raffcorreia/samsung-jog-api/memory/MEMORY.md

# Memory Index

- [Project Overview](project_overview.md) — CJ791 JOG emulator: phases 0–15 and 17–18 closed; Phase 16 parked pending hardware access; Phase 19 next for display usability/power hardening; Phase 7 KiCad in progress
- [No cd feedback](feedback_no_cd.md) — Never use cd; pass paths directly to commands (e.g. `npm test --prefix frontend/`)

**Deck UI (kiosk):** Phase 13 complete. Fixed widget geometry on **1280×800** — top bar `48px`, left JOG column `350px`, bottom log band `200px`. JOG and log regions do **not** resize each other when log text grows (scroll inside log). No portal/landing-page chrome; `pi-deck` naming lives in the status/version area, not duplicated as marketing chrome.

**Phase 13 UI decisions:** Clock uses `DSEG7 Classic` seven-segment font and is vertically centered within the unchanged top bar. Settings cog is top-right. LED is gray by default and blue only for future blink/feedback state, not steady `key_led_active`. Record button is a visual stub in the upper-right of the JOG widget column. OSD popup is a reusable portal-based template opened by the JOG dev trigger.

**Phase 14 live log:** Complete. Backend owns live log history in `LiveLogService` with a bounded `220`-entry replay buffer. WebSocket clients receive backend `log/entry` events and replay on connect; frontend only renders received backend entries. UI-originated stub messages go through `POST /api/v1/log`.

**JOG input:** The electrical jog path is **one direction at a time** (same as `JogDrive.release_all` before assert). The UI is **not** multitouch-parallel: a second finger is ignored while the first gesture is active. That matches hardware; it is not a multitouch gesture surface.
