raffcorreia/samsung-jog-api/docs/investigation/phase-24-full-matrix.md

# Phase 24 — Full Register Matrix

All 29 display configurations × 512 registers (256 DDC VCP codes + 256 I2C `0x58` registers).
Values are raw hex as captured. `-` = no scan data for this state/register combination.
DDC columns: VCP codes `0x00`–`0xFF`. I2C columns: `0x58` registers `0x00`–`0xFF`.

| State | DDC 0x0 | DDC 0x1 | DDC 0x2 | DDC 0x3 | DDC 0x4 | DDC 0x5 | DDC 0x6 | DDC 0x7 | DDC 0x8 | DDC 0x9 | DDC 0xa | DDC 0xb | DDC 0xc | DDC 0xd | DDC 0xe | DDC 0xf | DDC 0x10 | DDC 0x11 | DDC 0x12 | DDC 0x13 | DDC 0x14 | DDC 0x15 | DDC 0x16 | DDC 0x17 | DDC 0x18 | DDC 0x19 | DDC 0x1a | DDC 0x1b | DDC 0x1c | DDC 0x1d | DDC 0x1e | DDC 0x1f | DDC 0x20 | DDC 0x21 | DDC 0x22 | DDC 0x23 | DDC 0x24 | DDC 0x25 | DDC 0x26 | DDC 0x27 | DDC 0x28 | DDC 0x29 | DDC 0x2a | DDC 0x2b | DDC 0x2c | DDC 0x2d | DDC 0x2e | DDC 0x2f | DDC 0x30 | DDC 0x31 | DDC 0x32 | DDC 0x33 | DDC 0x34 | DDC 0x35 | DDC 0x36 | DDC 0x37 | DDC 0x38 | DDC 0x39 | DDC 0x3a | DDC 0x3b | DDC 0x3c | DDC 0x3d | DDC 0x3e | DDC 0x3f | DDC 0x40 | DDC 0x41 | DDC 0x42 | DDC 0x43 | DDC 0x44 | DDC 0x45 | DDC 0x46 | DDC 0x47 | DDC 0x48 | DDC 0x49 | DDC 0x4a | DDC 0x4b | DDC 0x4c | DDC 0x4d | DDC 0x4e | DDC 0x4f | DDC 0x50 | DDC 0x51 | DDC 0x52 | DDC 0x53 | DDC 0x54 | DDC 0x55 | DDC 0x56 | DDC 0x57 | DDC 0x58 | DDC 0x59 | DDC 0x5a | DDC 0x5b | DDC 0x5c | DDC 0x5d | DDC 0x5e | DDC 0x5f | DDC 0x60 | DDC 0x61 | DDC 0x62 | DDC 0x63 | DDC 0x64 | DDC 0x65 | DDC 0x66 | DDC 0x67 | DDC 0x68 | DDC 0x69 | DDC 0x6a | DDC 0x6b | DDC 0x6c | DDC 0x6d | DDC 0x6e | DDC 0x6f | DDC 0x70 | DDC 0x71 | DDC 0x72 | DDC 0x73 | DDC 0x74 | DDC 0x75 | DDC 0x76 | DDC 0x77 | DDC 0x78 | DDC 0x79 | DDC 0x7a | DDC 0x7b | DDC 0x7c | DDC 0x7d | DDC 0x7e | DDC 0x7f | DDC 0x80 | DDC 0x81 | DDC 0x82 | DDC 0x83 | DDC 0x84 | DDC 0x85 | DDC 0x86 | DDC 0x87 | DDC 0x88 | DDC 0x89 | DDC 0x8a | DDC 0x8b | DDC 0x8c | DDC 0x8d | DDC 0x8e | DDC 0x8f | DDC 0x90 | DDC 0x91 | DDC 0x92 | DDC 0x93 | DDC 0x94 | DDC 0x95 | DDC 0x96 | DDC 0x97 | DDC 0x98 | DDC 0x99 | DDC 0x9a | DDC 0x9b | DDC 0x9c | DDC 0x9d | DDC 0x9e | DDC 0x9f | DDC 0xa0 | DDC 0xa1 | DDC 0xa2 | DDC 0xa3 | DDC 0xa4 | DDC 0xa5 | DDC 0xa6 | DDC 0xa7 | DDC 0xa8 | DDC 0xa9 | DDC 0xaa | DDC 0xab | DDC 0xac | DDC 0xad | DDC 0xae | DDC 0xaf | DDC 0xb0 | DDC 0xb1 | DDC 0xb2 | DDC 0xb3 | DDC 0xb4 | DDC 0xb5 | DDC 0xb6 | DDC 0xb7 | DDC 0xb8 | DDC 0xb9 | DDC 0xba | DDC 0xbb | DDC 0xbc | DDC 0xbd | DDC 0xbe | DDC 0xbf | DDC 0xc0 | DDC 0xc1 | DDC 0xc2 | DDC 0xc3 | DDC 0xc4 | DDC 0xc5 | DDC 0xc6 | DDC 0xc7 | DDC 0xc8 | DDC 0xc9 | DDC 0xca | DDC 0xcb | DDC 0xcc | DDC 0xcd | DDC 0xce | DDC 0xcf | DDC 0xd0 | DDC 0xd1 | DDC 0xd2 | DDC 0xd3 | DDC 0xd4 | DDC 0xd5 | DDC 0xd6 | DDC 0xd7 | DDC 0xd8 | DDC 0xd9 | DDC 0xda | DDC 0xdb | DDC 0xdc | DDC 0xdd | DDC 0xde | DDC 0xdf | DDC 0xe0 | DDC 0xe1 | DDC 0xe2 | DDC 0xe3 | DDC 0xe4 | DDC 0xe5 | DDC 0xe6 | DDC 0xe7 | DDC 0xe8 | DDC 0xe9 | DDC 0xea | DDC 0xeb | DDC 0xec | DDC 0xed | DDC 0xee | DDC 0xef | DDC 0xf0 | DDC 0xf1 | DDC 0xf2 | DDC 0xf3 | DDC 0xf4 | DDC 0xf5 | DDC 0xf6 | DDC 0xf7 | DDC 0xf8 | DDC 0xf9 | DDC 0xfa | DDC 0xfb | DDC 0xfc | DDC 0xfd | DDC 0xfe | DDC 0xff | I2C 0x0 | I2C 0x1 | I2C 0x2 | I2C 0x3 | I2C 0x4 | I2C 0x5 | I2C 0x6 | I2C 0x7 | I2C 0x8 | I2C 0x9 | I2C 0xa | I2C 0xb | I2C 0xc | I2C 0xd | I2C 0xe | I2C 0xf | I2C 0x10 | I2C 0x11 | I2C 0x12 | I2C 0x13 | I2C 0x14 | I2C 0x15 | I2C 0x16 | I2C 0x17 | I2C 0x18 | I2C 0x19 | I2C 0x1a | I2C 0x1b | I2C 0x1c | I2C 0x1d | I2C 0x1e | I2C 0x1f | I2C 0x20 | I2C 0x21 | I2C 0x22 | I2C 0x23 | I2C 0x24 | I2C 0x25 | I2C 0x26 | I2C 0x27 | I2C 0x28 | I2C 0x29 | I2C 0x2a | I2C 0x2b | I2C 0x2c | I2C 0x2d | I2C 0x2e | I2C 0x2f | I2C 0x30 | I2C 0x31 | I2C 0x32 | I2C 0x33 | I2C 0x34 | I2C 0x35 | I2C 0x36 | I2C 0x37 | I2C 0x38 | I2C 0x39 | I2C 0x3a | I2C 0x3b | I2C 0x3c | I2C 0x3d | I2C 0x3e | I2C 0x3f | I2C 0x40 | I2C 0x41 | I2C 0x42 | I2C 0x43 | I2C 0x44 | I2C 0x45 | I2C 0x46 | I2C 0x47 | I2C 0x48 | I2C 0x49 | I2C 0x4a | I2C 0x4b | I2C 0x4c | I2C 0x4d | I2C 0x4e | I2C 0x4f | I2C 0x50 | I2C 0x51 | I2C 0x52 | I2C 0x53 | I2C 0x54 | I2C 0x55 | I2C 0x56 | I2C 0x57 | I2C 0x58 | I2C 0x59 | I2C 0x5a | I2C 0x5b | I2C 0x5c | I2C 0x5d | I2C 0x5e | I2C 0x5f | I2C 0x60 | I2C 0x61 | I2C 0x62 | I2C 0x63 | I2C 0x64 | I2C 0x65 | I2C 0x66 | I2C 0x67 | I2C 0x68 | I2C 0x69 | I2C 0x6a | I2C 0x6b | I2C 0x6c | I2C 0x6d | I2C 0x6e | I2C 0x6f | I2C 0x70 | I2C 0x71 | I2C 0x72 | I2C 0x73 | I2C 0x74 | I2C 0x75 | I2C 0x76 | I2C 0x77 | I2C 0x78 | I2C 0x79 | I2C 0x7a | I2C 0x7b | I2C 0x7c | I2C 0x7d | I2C 0x7e | I2C 0x7f | I2C 0x80 | I2C 0x81 | I2C 0x82 | I2C 0x83 | I2C 0x84 | I2C 0x85 | I2C 0x86 | I2C 0x87 | I2C 0x88 | I2C 0x89 | I2C 0x8a | I2C 0x8b | I2C 0x8c | I2C 0x8d | I2C 0x8e | I2C 0x8f | I2C 0x90 | I2C 0x91 | I2C 0x92 | I2C 0x93 | I2C 0x94 | I2C 0x95 | I2C 0x96 | I2C 0x97 | I2C 0x98 | I2C 0x99 | I2C 0x9a | I2C 0x9b | I2C 0x9c | I2C 0x9d | I2C 0x9e | I2C 0x9f | I2C 0xa0 | I2C 0xa1 | I2C 0xa2 | I2C 0xa3 | I2C 0xa4 | I2C 0xa5 | I2C 0xa6 | I2C 0xa7 | I2C 0xa8 | I2C 0xa9 | I2C 0xaa | I2C 0xab | I2C 0xac | I2C 0xad | I2C 0xae | I2C 0xaf | I2C 0xb0 | I2C 0xb1 | I2C 0xb2 | I2C 0xb3 | I2C 0xb4 | I2C 0xb5 | I2C 0xb6 | I2C 0xb7 | I2C 0xb8 | I2C 0xb9 | I2C 0xba | I2C 0xbb | I2C 0xbc | I2C 0xbd | I2C 0xbe | I2C 0xbf | I2C 0xc0 | I2C 0xc1 | I2C 0xc2 | I2C 0xc3 | I2C 0xc4 | I2C 0xc5 | I2C 0xc6 | I2C 0xc7 | I2C 0xc8 | I2C 0xc9 | I2C 0xca | I2C 0xcb | I2C 0xcc | I2C 0xcd | I2C 0xce | I2C 0xcf | I2C 0xd0 | I2C 0xd1 | I2C 0xd2 | I2C 0xd3 | I2C 0xd4 | I2C 0xd5 | I2C 0xd6 | I2C 0xd7 | I2C 0xd8 | I2C 0xd9 | I2C 0xda | I2C 0xdb | I2C 0xdc | I2C 0xdd | I2C 0xde | I2C 0xdf | I2C 0xe0 | I2C 0xe1 | I2C 0xe2 | I2C 0xe3 | I2C 0xe4 | I2C 0xe5 | I2C 0xe6 | I2C 0xe7 | I2C 0xe8 | I2C 0xe9 | I2C 0xea | I2C 0xeb | I2C 0xec | I2C 0xed | I2C 0xee | I2C 0xef | I2C 0xf0 | I2C 0xf1 | I2C 0xf2 | I2C 0xf3 | I2C 0xf4 | I2C 0xf5 | I2C 0xf6 | I2C 0xf7 | I2C 0xf8 | I2C 0xf9 | I2C 0xfa | I2C 0xfb | I2C 0xfc | I2C 0xfd | I2C 0xfe | I2C 0xff |
| --- | --- | --- | --- | --- | --- | --- | --- | --- | --- | --- | --- | --- | --- | --- | --- | --- | --- | --- | --- | --- | --- | --- | --- | --- | --- | --- | --- | --- | --- | --- | --- | --- | --- | --- | --- | --- | --- | --- | --- | --- | --- | --- | --- | --- | --- | --- | --- | --- | --- | --- | --- | --- | --- | --- | --- | --- | --- | --- | --- | --- | --- | --- | --- | --- | --- | --- | --- | --- | --- | --- | --- | --- | --- | --- | --- | --- | --- | --- | --- | --- | --- | --- | --- | --- | --- | --- | --- | --- | --- | --- | --- | --- | --- | --- | --- | --- | --- | --- | --- | --- | --- | --- | --- | --- | --- | --- | --- | --- | --- | --- | --- | --- | --- | --- | --- | --- | --- | --- | --- | --- | --- | --- | --- | --- | --- | --- | --- | --- | --- | --- | --- | --- | --- | --- | --- | --- | --- | --- | --- | --- | --- | --- | --- | --- | --- | --- | --- | --- | --- | --- | --- | --- | --- | --- | --- | --- | --- | --- | --- | --- | --- | --- | --- | --- | --- | --- | --- | --- | --- | --- | --- | --- | --- | --- | --- | --- | --- | --- | --- | --- | --- | --- | --- | --- | --- | --- | --- | --- | --- | --- | --- | --- | --- | --- | --- | --- | --- | --- | --- | --- | --- | --- | --- | --- | --- | --- | --- | --- | --- | --- | --- | --- | --- | --- | --- | --- | --- | --- | --- | --- | --- | --- | --- | --- | --- | --- | --- | --- | --- | --- | --- | --- | --- | --- | --- | --- | --- | --- | --- | --- | --- | --- | --- | --- | --- | --- | --- | --- | --- 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
| Single: TB | - | - | 0x02 | - | - | - | - | - | - | - | - | 0x32 | 40 | - | - | - | 59 | - | 75 | - | 0x04 | - | 70 | - | 70 | - | 70 | - | - | - | - | - | - | - | - | - | - | - | - | - | - | - | - | - | - | - | - | - | - | - | - | - | - | - | - | - | - | - | - | - | - | - | - | - | - | - | - | - | - | - | - | - | - | - | - | - | - | - | - | - | - | - | 0x00 | - | - | - | - | - | - | - | - | - | - | - | - | - | 0x04 | - | 3 | - | - | - | - | - | - | - | - | - | 50 | - | 50 | - | 50 | - | - | - | - | - | - | - | - | - | - | - | - | - | - | - | - | - | - | - | - | - | - | - | - | - | - | - | - | 0x02 | - | - | - | - | - | - | - | - | - | - | - | - | - | - | - | - | - | - | - | - | - | - | - | - | - | - | - | - | 0x00 | - | 23364 | - | 6010 | - | - | - | 0x01 | - | - | - | 0x03 | - | - | - | - | - | - | - | - | - | 200 | - | - | - | - | - | 0x6F | - | 0x12 | 0x20 | 0x02 | - | 0x02 | - | - | - | - | - | - | - | - | - | 0x01 | - | - | - | - | - | 0x02 | - | - | 0x01 | - | - | - | - | - | - | - | - | - | - | - | - | - | - | - | - | - | - | - | - | - | - | - | - | - | - | - | - | - | - | 0x02 | 0x00 | 0x0 | 0x0 | 0x79 | 0x0 | 0x0 | 0x0 | 0x0 | 0x37 | 0x37 | 0x0 | 0x0 | 0x81 | 0xd3 | 0x0 | 0x4 | 0xe0 | 0x3 | 0x13 | 0x0 | 0x0 | 0x0 | 0x0 | 0x0 | 0x0 | 0x0 | 0x0 | 0x0 | 0x0 | 0x0 | 0x0 | 0x0 | 0xee | 0x0 | 0x10 | 0x3 | 0xff | 0x0 | 0x0 | 0x0 | 0x0 | 0x0 | 0x0 | 0x20 | 0x0 | 0x0 | 0x5 | 0x0 | 0x0 | 0x0 | 0x0 | 0x50 | 0x0 | 0x40 | 0x0 | 0x2 | 0x0 | 0x0 | 0x0 | 0x0 | 0x45 | 0xd3 | 0xc7 | 0x6 | 0x0 | 0x84 | 0x84 | 0x84 | 0x0 | 0x0 | 0x0 | 0x0 | 0x9 | 0xf | 0x6 | 0x2 | 0x40 | 0x0 | 0x8 | 0x0 | 0x0 | 0x0 | 0x0 | 0x0 | 0x0 | 0x0 | 0x0 | 0x0 | 0x0 | 0x0 | 0x0 | 0x0 | 0x0 | 0x0 | 0x0 | 0x0 | 0x0 | 0x0 | 0x1 | 0x0 | 0x0 | 0x0 | 0x0 | 0x0 | 0x0 | 0x0 | 0x0 | 0x0 | 0x0 | 0x0 | 0x0 | 0x0 | 0x0 | 0x50 | 0x0 | 0x0 | 0x20 | 0x0 | 0x0 | 0x0 | 0x0 | 0x3 | 0x0 | 0x0 | 0x0 | 0x0 | 0x0 | 0x0 | 0x0 | 0x0 | 0x0 | 0x0 | 0x0 | 0x0 | 0x0 | 0x0 | 0x0 | 0x0 | 0x0 | 0x0 | 0x0 | 0x0 | 0x0 | 0x0 | 0x0 | 0x0 | 0x0 | 0x0 | 0x0 | 0x0 | 0x0 | 0xc0 | 0x0 | 0x0 | 0x0 | 0x0 | 0x0 | 0x0 | 0x0 | 0x0 | 0x4 | 0xef | 0x21 | 0xff | 0xd8 | 0x0 | 0x0 | 0xff | 0xf8 | 0x0 | 0x0 | 0x0 | 0x0 | 0x0 | 0x0 | 0x2 | 0x0 | 0x0 | 0x0 | 0x4 | 0x0 | 0x0 | 0x0 | 0x3 | 0x0 | 0x0 | 0x0 | 0x0 | 0x0 | 0x1 | 0x13 | 0x6f | 0xb | 0x0 | 0x0 | 0x0 | 0x0 | 0x0 | 0x0 | 0x41 | 0x66 | 0x66 | 0x0 | 0x0 | 0x0 | 0x0 | 0x0 | 0x0 | 0x0 | 0x0 | 0x0 | 0x0 | 0x0 | 0x0 | 0x0 | 0x0 | 0x3 | 0x3 | 0x3 | 0x3 | 0x3 | 0x3 | 0x3 | 0x3 | 0x3 | 0xf4 | 0x0 | 0x0 | 0x0 | 0x0 | 0x0 | 0x0 | 0x0 | 0x0 | 0x0 | 0x0 | 0x0 | 0x0 | 0x0 | 0x0 | 0x0 | 0x10 | 0x32 | 0x54 | 0x76 | 0x10 | 0x32 | 0x54 | 0x98 | 0x10 | 0x32 | 0x54 | 0x76 | 0x0 | 0x0 | 0x1 | 0x45 |
| PBP — DP left / HDMI right | - | - | 0x02 | - | - | - | - | - | - | - | - | 0x32 | 40 | - | - | - | 0x3B | - | 0x4B | - | 0x04 | - | 70 | - | 70 | - | 70 | - | - | - | - | - | - | - | - | - | - | - | - | - | - | - | - | - | - | - | - | - | - | - | - | - | - | - | - | - | - | - | - | - | - | - | - | - | - | - | - | - | - | - | - | - | - | - | - | - | - | - | - | - | - | - | 0x00 | - | - | - | - | - | - | - | - | - | - | - | - | - | 0x03 | - | 0x03 | - | - | - | - | - | - | - | - | - | 50 | - | 50 | - | 50 | - | - | - | - | - | - | - | - | - | - | - | - | - | - | - | - | - | - | - | - | - | - | - | - | - | - | - | - | 0x02 | - | - | - | - | - | - | - | - | - | - | - | - | - | - | - | - | - | - | - | - | - | - | - | - | - | - | - | - | 0x00 | - | 23364 | - | 6010 | - | - | - | 0x01 | - | - | - | 0x03 | - | - | - | - | - | - | - | - | - | 200 | - | - | - | - | - | 0x6F | - | 0x12 | 0x20 | 0x02 | - | 0x02 | - | - | - | - | - | - | - | - | - | 0x01 | - | - | - | - | - | 0x02 | - | - | 0x01 | - | - | - | - | - | - | - | - | - | - | - | - | - | - | - | - | - | - | - | - | - | - | - | - | - | - | - | - | - | - | 0x02 | 0x00 | 0x00 | 0x00 | 0x79 | 0x00 | 0x00 | 0x00 | 0x00 | 0x37 | 0x37 | 0x00 | 0x00 | 0x81 | 0xD3 | 0xFF | 0x04 | 0xE0 | 0x03 | 0x13 | 0x00 | 0x00 | 0x00 | 0x00 | 0x00 | 0x00 | 0x00 | 0x00 | 0x00 | 0x00 | 0x00 | 0x00 | 0x00 | 0xEE | 0x00 | 0x10 | 0x03 | 0xFF | 0x00 | 0x00 | 0x00 | 0x00 | 0x00 | 0x00 | 0x20 | 0x00 | 0x00 | 0x05 | 0x00 | 0x00 | 0x00 | 0x00 | 0x50 | 0x00 |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
