raffcorreia/samsung-jog-api/docs/implementation/phase-22-execution.md

# Phase 22 Execution Record

## Purpose

Track **Phase 22: Physical Display and Pi Power Button** per [Implementation Plan](./plan.md).

## Status

**Complete.** Closed 2026-05-01 at deploy r89 (v0.1.9).

## Working Goal

Define and validate a physical local power-control path: a hardware button for display on/off and a practical strategy for physically waking or powering on the Raspberry Pi when software UI is unavailable.

## Key Questions to Resolve

1. What should one physical button do — display toggle only, or also Pi shutdown/wake?
2. How does Pi 5 handle a physical power button natively?
3. What is the equivalent path for Pi 2?
4. Single button or separate buttons for display vs Pi power?
5. How does the physical button relate to the existing software PowerMenu?

## Pi 5 — Native Power Button Interface

Raspberry Pi 5 has a dedicated **J2** 2-pin header (`PWR_BTN` / `GLOBAL_EN`) wired to the MxL7704 PMIC:

- **While running:** short press triggers a clean OS shutdown (PMIC signals halt)
- **While halted/off:** any press wakes and boots the Pi
- No software configuration required — behaviour is handled entirely by the PMIC and RP1 chip
- A momentary normally-open button across J2 is sufficient

This is the cleanest path: wire one button to J2 and the Pi handles shutdown and wake natively.

## Pi 2 — Power Button Interface

Raspberry Pi 2 has no PMIC or native power-button header. Available options:

| Option | What it does | Limitation |
|---|---|---|
| **RUN pin header** | Resets the CPU (equivalent to pulling RESET low) | Not a clean shutdown; does not wake from a software halt |
| **GPIO shutdown button** | GPIO + software daemon triggers clean shutdown | Cannot wake from halt — Pi is off, GPIO ISR is not running |
| **External power supervisor** | Always-on MCU or relay cuts/restores 5V to Pi | Requires additional always-on hardware circuit |
| **Operational limitation** | Document that Pi 2 must be woken by restoring USB-C power | No extra hardware needed; operator must physically unplug/replug |

## Decisions

_To be filled in during phase execution._

## GPIO Assignments (Phase 22 additions)

| Signal | GPIO (BCM) | Physical pin | Direction |
|---|---|---|---|
| `display_btn` — display toggle button (active low) | GPIO4 | 7 | Input |
| `led_data` — WS2812B LED data out (SPI0 MOSI) | GPIO10 | 19 | Output |

GPIO10 (SPI0 MOSI) is used for WS2812B because Pi 5's RP1 chip does not expose the GPU DMA mailbox required by `rpi_ws281x`.  The SPI bus encodes each WS2812B bit as 8 SPI clock cycles at 6.4 MHz (156.25 ns/cycle), producing the required NRZ waveform entirely in hardware without root or DMA access.  SPI is accessible via `/dev/spidev0.0` on Pi 5.  On Pi 4 and earlier, SPI0 is on the same GPIO10 pin — no wiring change needed between Pi generations.

## Component Designator Map (Phase 22 protoboard additions)

Continues the Phase 21 numbering (last used: Q9, R24, C4, no U or SW designators before this phase).

| Ref | Value | Function |
|-----|---|---|
| `SW1` | Momentary SPST NO | Display toggle button (GPIO4 → GND when pressed) |
| `R25` | 10 kΩ | GPIO4 hardware pull-up to 3.3V |
| `C5` | 100 nF | GPIO4 debounce cap to GND |
| `U2` | SN74AHCT125 | 3.3V→5V level shifter — **removed**; caused random frame corruption. WS2812B driven directly from GPIO10 at 3.3V logic. |

## Protoboard Wiring — Button Circuit

```
+3V3 (pin 1) ──── R25 (10 kΩ) ──── GPIO4 (pin 7) ──── SW1 ──── GND
                                         │
                                    C5 (100 nF)
                                         │
                                        GND
```

- R25: pull-up keeps GPIO4 HIGH when button is not pressed.
- SW1: connects GPIO4 to GND when pressed (active-low input).
- C5: debounce; 100 nF across GPIO4-GND smooths mechanical contact bounce.
- Software uses `gpiozero.Button(4)` with `pull_up=True` (internal + external pull-up).

## Protoboard Wiring — LED Direct Wiring

```
GPIO10 (pin 19, SPI0 MOSI) ──── LED DIN

LED GND → GND rail
LED 5V → 5V rail
```

- GPIO10 drives WS2812B DIN directly at 3.3V logic — no level shifter.
- The SN74AHCT125 level shifter (U2) was removed after testing showed it caused random frame corruption and missed LED updates. WS2812B tolerates 3.3V logic reliably at this cable length.
- Pi 5 uses SPI (not DMA/PWM) because RP1 has no GPU mailbox; `StripDriver` uses `spidev` at 6.4 MHz.
- Each WS2812B bit is encoded as 8 SPI clock cycles (Adafruit NeoPixel encoding: `0xF8`='1', `0xC0`='0').
- Protoboard signal integrity may still be a factor; if corruption returns, consider point-to-point wiring directly from the Pi header to LED DIN.

## PowerMenu Redesign

### Action Dialog

Replace the current two-option dialog (Display / Power off) with three options:

| Option | Size | Behavior |
|---|---|---|
| **Display only** | normal | toggle display on/off (existing path) |
| **Reset** | small | navigate to countdown screen (10 s) → reboot |
| **Power off** | small, dangerous | navigate to confirmation screen → countdown screen (10 s) → halt |

### Confirmation Screen (reusable)

Shown before Power off only. Text must explain that the deck **cannot be restored without physically unplugging and replugging power**. Screen must be implemented as a reusable component parameterized by message, confirm label, and on-confirm action.

### Countdown Screen (reusable — single component)

Single countdown component used by both Reset and Power off paths. Parameters:
- duration (10 s for both actions; previously may have been shorter)
- on-complete action (reboot | halt)
- cancelable (user can go back before countdown expires)

No duplicate countdown screens.

## Evidence Checklist

- ✅ Pi 5 power button behavior defined and documented (J2 header / PMIC — clean shutdown while running, wake from halt)
- ✅ Pi 2 power button strategy decided (operational limitation documented — physically unplug/replug power)
- ✅ Display on/off button wiring defined (SW1 on GPIO4, R25 pull-up, C5 debounce)
- ✅ Single button decided — SW1 handles display toggle; Pi 5 J2 handles Pi power separately
- ✅ Debounce and press-duration requirements defined (hardware RC filter + 50 ms software debounce; 3 s hold threshold)
- ✅ Physical button design does not conflict with GPIO24 display circuit (GPIO4 is independent)
- ✅ PowerMenu action dialog updated: Display / Restart / Power off with correct sizing
- ✅ Power off confirmation uses `ConfirmDialog` component
- ✅ Countdown screen is a single reusable component (10 s, parameterized by action)
- ✅ Reset path: dialog → countdown → reboot works end-to-end
- ✅ Power off path: dialog → confirmation → countdown → halt works end-to-end
- ✅ WS2812B wired on GPIO10 (SPI0 MOSI, pin 19) direct — level shifter removed (caused corruption)
- ✅ `StripDriver` implemented via SPI at 6.4 MHz with per-LED lock arbitration
- ✅ Healthy state (solid green) confirmed on hardware at startup
- ✅ `StripDriver` integrated into service lifecycle; physical button broadcasts deck-only
- ✅ Host health gate passes (verified at close — see snapshot below)

## Host Health Snapshot

Captured 2026-05-01 at deploy r89 (v0.1.9), ~41 min uptime, kiosk idle:

```text
temperature:    49.4 °C
get_throttled:  0x0  (no flags)
uptime:         41 min
load average:   0.33 / 0.14 / 0.09
RAM:            15 GiB total, 773 MiB used, 15 GiB available
swap:           2.0 GiB total, 0 used
disk (/):       58 GiB total, 5.7 GiB used (11%)
pi-deck:        0.1.9+r89, hardware=live, control_state=idle
```

## Power Consumption

Measured 2026-05-01 with protoboard attached (SW1, WS2812B LED, Phase 21 display circuit):

Measurements taken at 5V supply with Pi 5, protoboard, and Waveshare DSI display. Current fluctuates continuously; values are approximate averages.

| Condition | Voltage | Current | Power | Notes |
|---|---|---|---|---|
| Display ON 100%, LED green 100%, 1 browser | 5V | ~1.30A | ~6.5W | |
| Display ON 100%, LED green 1%, 1 browser | 5V | ~1.26A | ~6.3W | LED at 100% adds ~40 mA |
| Display ON 100%, LED green 1%, no browser  | 5V | ~1.22A | ~6.1W | ~40 mA saved closing remote WS connection |
| JOG button press (any direction) | 5V | ~1.47A | ~7.4W | ~250 mA spike during drive actuation; brief |

The JOG spike (~250 mA over idle) is caused by the GPIO drive circuit actuating the monitor's control board contacts. The spike is well within the 3A supply headroom and does not destabilize the Pi. A decoupling capacitor on the Pi's 5V rail is not needed — the supply has ample margin. A 100 µF electrolytic near the drive transistors on the custom PCB is worth adding as a precaution (noted in Phase 7 open items).
