raffcorreia/samsung-jog-api/docs/implementation/phase-4-execution.md

# Phase 4 Execution Record

## Purpose

This document records the execution outcome for `Phase 4: Analog Drive Circuit Design`.

It complements:

- [Implementation Plan](../implementation/plan.md)
- [Solution Overview](../design/solution-overview.md)
- [Phase 2 Execution Record](./phase-2-execution.md)
- [Phase 3 Execution Record](./phase-3-execution.md)
- [Phase 4 Analog Drive BOM](../hardware/analog-drive-bom.md)

## Goal

Design and approve an analog drive path that can safely reproduce the required `JOG` resistor-to-ground states on `KEY_ADC1` and `KEY_ADC2` while preserving the original front-panel `JOG` behavior.

## Reference Diagram

Current analog-drive concept diagram:

Phase 4 analog drive path concept

KiCad design artifacts for implementation:

- KiCad project: [`hardware/kicad/analog-drive/analog-drive.kicad_pro`](../../hardware/kicad/analog-drive/analog-drive.kicad_pro)
- KiCad schematic: [`hardware/kicad/analog-drive/analog-drive.kicad_sch`](../../hardware/kicad/analog-drive/analog-drive.kicad_sch)
- KiCad PCB: [`hardware/kicad/analog-drive/analog-drive.kicad_pcb`](../../hardware/kicad/analog-drive/analog-drive.kicad_pcb)
- KiCad BOM CSV: [`hardware/kicad/analog-drive/analog-drive.bom.csv`](../../hardware/kicad/analog-drive/analog-drive.bom.csv)

## Inputs From Prior Phases

The design is based on these already-confirmed constraints:

- `KEY_ADC1` and `KEY_ADC2` are interpreted by the monitor as resistance-to-ground states.
- `KEY_ADC1` is effectively binary (`idle` vs `center`).
- `KEY_ADC2` requires multiple distinct analog states (`idle`, `left`, `right`, `down`, `up`).
- the original `JOG` board remains physically present and must continue to function.
- observation and drive paths must coexist without bus contention.

## Design Scope

In scope:

- analog drive architecture for `KEY_ADC1` and `KEY_ADC2`
- drive/observe coexistence strategy
- preservation strategy for original `JOG` behavior
- component selection for the drive subcircuit
- analog-drive BOM and review artifacts

Out of scope:

- final integrated board outline and connector families
- final software API surface
- final GPIO numbering decisions

## Candidate Drive Approaches

### Candidate A: GPIO-Selected Discrete Resistor Ladder

Use analog switches to connect pre-selected resistor legs to ground per command.

Pros:

- deterministic resistance states
- straightforward debug with DMM
- minimal software complexity

Cons:

- more passives and routing density
- tolerance-stack management across many discrete values

### Candidate B: Digital Potentiometer Per Channel

Use one digital potentiometer channel per driven signal.

Pros:

- compact resistor-state control via software
- fewer discrete resistor networks

Cons:

- wiper behavior and endpoint resistance may reduce state fidelity
- update timing and nonlinearity may complicate repeatability

### Candidate C: Fail-Safe Per-Leg Analog Switch Drive (Selected)

Use one normally-open analog switch per resistor leg so every commanded resistance-to-ground path is individually off by default.

Pros:

- best fit to asymmetric signal behavior (`KEY_ADC2` multi-state, `KEY_ADC1` binary)
- hardware-default safe state does not depend on mux address decoding during Pi boot or reset
- predictable electrical states with low software ambiguity
- preserves a clear path to later calibration refinement

Cons:

- uses more switch-control GPIOs than a mux-based design
- slightly higher part count than a shared-address mux approach

## Selected Architecture

The selected Phase 4 architecture is a **fail-safe per-leg switched-resistance drive path**:

- `KEY_ADC2`: four independent bilateral analog-switch channels gate four calibrated resistor legs to `GND`, one per logical direction.
- `KEY_ADC1`: dedicated single bilateral analog switch gates the center pull-down leg.
- both channels default to high-impedance (`idle`) when no command is active.
- one command arbiter guarantees mutually exclusive drive state application.
- hardware biasing holds all switch enables in the off state until the host actively asserts a command.
- software-enforced break-before-make timing remains in place as a second line of protection.

## Original `JOG` Preservation Strategy

The original front-panel `JOG` remains connected in parallel with the controller board under these rules:

- controller outputs are never actively driven high onto monitor lines.
- controller only presents controlled resistance-to-ground states.
- controller defaults to high-impedance when idle or faulted.
- firmware arbitration blocks controller-driven actions while local physical manipulation is detected as active.

## Drive/Observe Coexistence Strategy

- observation front end remains high-impedance and passive relative to drive operations.
- software continuously verifies observed line values during drive operations.
- if observed voltages fall outside expected windows, drive is immediately released to high-impedance and the sequence is aborted.

## Verification Approach

The Phase 4 verification approach is:

1. bench-check each commanded resistor state at the monitor-side connector with power off.
2. verify powered-state voltages for each commanded logical action.
3. validate that local `JOG` operation still works with the drive board connected.
4. run repeated command cycles while confirming no stuck-active drive condition.
5. confirm safe release-to-idle behavior on host process termination.

## Deliverables Completed

- reviewed analog-drive topology with explicit switch-to-resistor channel mapping
- cleaned KiCad schematic with explicit monitor and host connector wiring
- corrected the final `KEY_ADC1_BUS`, `KEY_ADC2_BUS`, and connector-ground net assignments in the KiCad schematic
- compact KiCad PCB prototype layout for the analog-drive subcircuit
- attached standard KiCad 3D models to the PCB footprints so populated board rendering works again
- JLC-oriented BOM using tested commercial resistor substitutions and current orderable part numbers
- exported manufacturing artifacts validated by `kicad-cli` gerber, position-file, and board-render generation

## Exit-Criteria Assessment

Phase 4 is complete at the prototype-design level.

The final state now includes:

- a KiCad schematic with explicit monitor and host connector wiring
- a routed KiCad PCB prototype for the analog-drive circuit
- a JLC-oriented BOM for the tested resistor set
- manufacturing artifact export from the board file
- working 3D model references on the PCB footprints

Verification status:

- `kicad-cli sch erc` passes with `0` errors and only library/symbol warnings
- `kicad-cli pcb export gerbers` succeeds
- `kicad-cli pcb export pos` succeeds
- `kicad-cli pcb render` succeeds

Known limitation:

- `kicad-cli pcb drc` crashes in this environment with a KiCad `10.0.0` macOS CLI runtime error (`SwiftNativeNSArray` out-of-range), so a final GUI DRC pass is still required before sending the board to fabrication
- one remaining schematic warning cluster in the `ADC1_CENTER_EN` area should still be reviewed visually in KiCad GUI during the final PCB pass

## Open Items Deferred to Later Phases

- final integrated-board connector and mechanical constraints
- exact software timing constants after hardware-in-loop testing
- validation of the JLC-orderable `U1` substitution on the physical assembled board
- final GUI PCB DRC and visual routing review before fabrication release
