raffcorreia/samsung-jog-api/docs/implementation/phase-17-execution.md

# Phase 17 Execution Record

## Purpose

Record completion of **Phase 17: Development Fixture** per [Implementation Plan](./plan.md).

## Status

**Closed:** 2026-04-20.

Phase 17 was closed as a pragmatic temporary fixture, not as a detailed mechanical-design deliverable.

## Summary

A crude open support was built to keep the monitor and Raspberry Pi together in a repeatable development setup. The fixture is intentionally minimal: it is only meant to hold the monitor/control-deck assembly in a usable position while the project moves into display and touch validation.

The result is sufficient to unblock Phase 18 because the Pi and monitor can now be handled and tested as one development assembly instead of as loose bench hardware.

## Scope Notes

- The fixture is open and temporary.
- The fixture does not attempt final enclosure geometry, cosmetic finish, protective covers, or detailed cable-management design.
- Connector-clearance and strain-relief work remains practical/observational rather than fully documented CAD-level validation.
- Any final enclosure, refined mount, or integrated-board mechanical layout remains deferred.

## Exit Criteria Review

| Criterion | Status |
|---|---|
| Pi and development hardware are held in a stable, repeatable position | Done for temporary development use. |
| Connectors remain serviceable without full disassembly | Accepted for current crude support. Re-check during Phase 18 display installation. |
| Harness routing avoids obvious strain during development handling | Accepted for current crude support. Re-check once DSI display and touch wiring are installed. |
| Pi orientation and detailed clearance rationale are documented | Deferred. The Phase 17 deliverable was intentionally reduced to a crude support so Phase 18 can proceed. |

## Follow-Up

- Re-check cable strain and connector access after the Waveshare display is physically installed.
- Capture any display-specific mechanical constraints in the Phase 18 execution record.
- Defer polished enclosure, covers, and final integrated-board mechanical design to a later enclosure/mechanical phase.
