raffcorreia/samsung-jog-api/docs/investigation/ddc-scan/ddc-scan-20260501-153903-summary.md

# DDC VCP Scan Summary

- **Date:** 2026-05-01 15:43
- **Bus:** I2C-13
- **Codes scanned:** 256 (0x00–0xFF)
- **Codes responding:** 32
- **Log:** `ddc-scan-20260501-153903.jsonl`

## Responding Codes

| Code | Name | Type | Current | Max / SL |
|---|---|---|---|---|
| `0x02` | New Control Value | CNC |  | VCP 02 CNC x00 xff x00 x02 |
| `0x0B` | Color Temperature Increment | CNC |  | VCP 0B CNC xff xff x00 x32 |
| `0x0C` | Color Temperature Request | C | 40 | 170 |
| `0x10` | Brightness | C | 59 | 100 |
| `0x12` | Contrast | C | 75 | 100 |
| `0x14` | Select Color Preset | SNC |  | VCP 14 SNC x04 |
| `0x16` | Red Video Gain | C | 70 | 100 |
| `0x18` | Green Video Gain | C | 70 | 100 |
| `0x1A` | Blue Video Gain | C | 70 | 100 |
| `0x52` | Active Control | CNC |  | VCP 52 CNC x00 xff x00 x00 |
| `0x60` | Input Source | SNC |  | VCP 60 SNC x04 |
| `0x62` | Audio Speaker Volume | C | 3 | 100 |
| `0x6C` | Video Black Level: Red | C | 50 | 100 |
| `0x6E` | Video Black Level: Green | C | 50 | 100 |
| `0x70` | Video Black Level: Blue | C | 50 | 100 |
| `0x8D` | Audio Mute | SNC |  | VCP 8D SNC x02 |
| `0xAA` | Screen Orientation | SNC |  | VCP AA SNC x00 |
| `0xAC` | Horizontal Frequency | C | 23364 | 65281 |
| `0xAE` | Vertical Frequency | C | 6000 | 65535 |
| `0xB2` | Flat Panel Sub-Pixel Layout | SNC |  | VCP B2 SNC x01 |
| `0xB6` | Display Technology Type | SNC |  | VCP B6 SNC x03 |
| `0xC0` | Display Usage Time | C | 200 | 65535 |
| `0xC6` | Application Enable Key | CNC |  | VCP C6 CNC xff xff x00 x6f |
| `0xC8` | Display Controller ID | CNC |  | VCP C8 CNC xff xff x00 x12 |
| `0xC9` | Display Firmware Level | CNC |  | VCP C9 CNC xff xff x01 x20 |
| `0xCA` | OSD/Button Control | SNC |  | VCP CA SNC x02 |
| `0xCC` | OSD Language | SNC |  | VCP CC SNC x02 |
| `0xD6` | Power Mode | SNC |  | VCP D6 SNC x01 |
| `0xDC` | Display Application | SNC |  | VCP DC SNC x02 |
| `0xDF` | VCP Version | CNC |  | VCP DF CNC xff xff x02 x01 |
| `0xFE` | Unknown (0xFE) | CNC |  | VCP FE CNC x00 x02 x00 x02 |
| `0xFF` | Unknown (0xFF) | CNC |  | VCP FF CNC x00 x01 x00 x00 |

*Generated by `tools/scripts/ddc-scan.py`*
