raffcorreia/samsung-jog-api/docs/investigation/ddc-scan/ddc-scan-20260501-161242-summary.md

# DDC VCP Scan Summary

- **Date:** 2026-05-01 16:14
- **Bus:** I2C-13
- **Codes scanned:** 256 (0x00–0xFF)
- **Codes responding:** 0
- **Log:** `ddc-scan-20260501-161242.jsonl`

## Responding Codes

| Code | Name | Type | Current | Max / SL |
|---|---|---|---|---|

*Generated by `tools/scripts/ddc-scan.py`*
