raffcorreia/samsung-jog-api/docs/investigation/i2c-scan/pip-size3-tb-small-hdmi-main/i2c-scan-20260501-233134-ddc-summary.md

# DDC VCP Scan — Device 0x37 (via DDC/CI protocol)

- **Date:** 2026-05-01 23:31

| VCP | Name | Current | Max | Status |
|-----|---|---|-----|---|
| `0x10` | Brightness | `0x3B` | `0x64` | ok |
| `0x12` | Contrast | `0x4B` | `0x64` | ok |
| `0x60` | Input Source | `0x01` | `0x03` | ok |
| `0x62` | Audio Speaker Volume | `0x03` | `0x64` | ok |
| `0xD6` | Power Mode | `0x01` | `0x04` | ok |
| `0xDC` | Display Application | `0x02` | `0x03` | ok |

*Generated by `tools/scripts/collect-register-capture.py`*
