raffcorreia/samsung-jog-api/docs/investigation/bus-discovery/20260504-161706-single-source-tb-summary.md

# Monitor Bus Discovery Summary

- **Captured at:** 2026-05-04T16:17:06+00:00
- **Bus:** /dev/i2c-13
- **State:** Single source: TB
- **Responding addresses:** 5

| Address | Classification | Readable | Errors |
|---|---|---|---|
| `0x37` | partial_map | 244/256 | 12 |
| `0x3A` | full_map | 256/256 | 0 |
| `0x50` | full_map | 256/256 | 0 |
| `0x54` | full_map | 256/256 | 0 |
| `0x58` | full_map | 256/256 | 0 |
