raffcorreia/samsung-jog-api/hardware/kicad/hdmi-ddc-intermediary/hdmi-ddc-intermediary-back.png

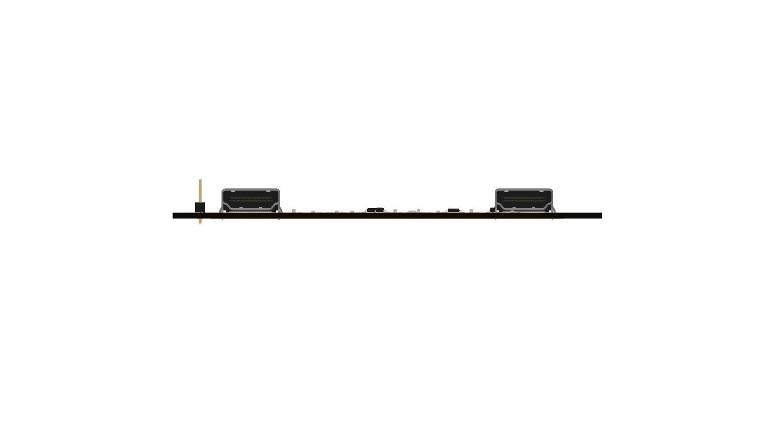
hardware/kicad/hdmi-ddc-intermediary/hdmi-ddc-intermediary-back.png
